gerarduscalcitrosus/shroompi/docs/camera_module.jpg

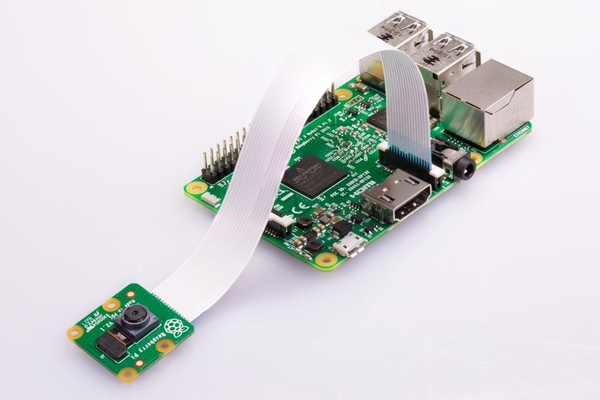
docs/camera_module.jpg
