gerarduscalcitrosus/shroompi/docs/prototypinghat.jpg

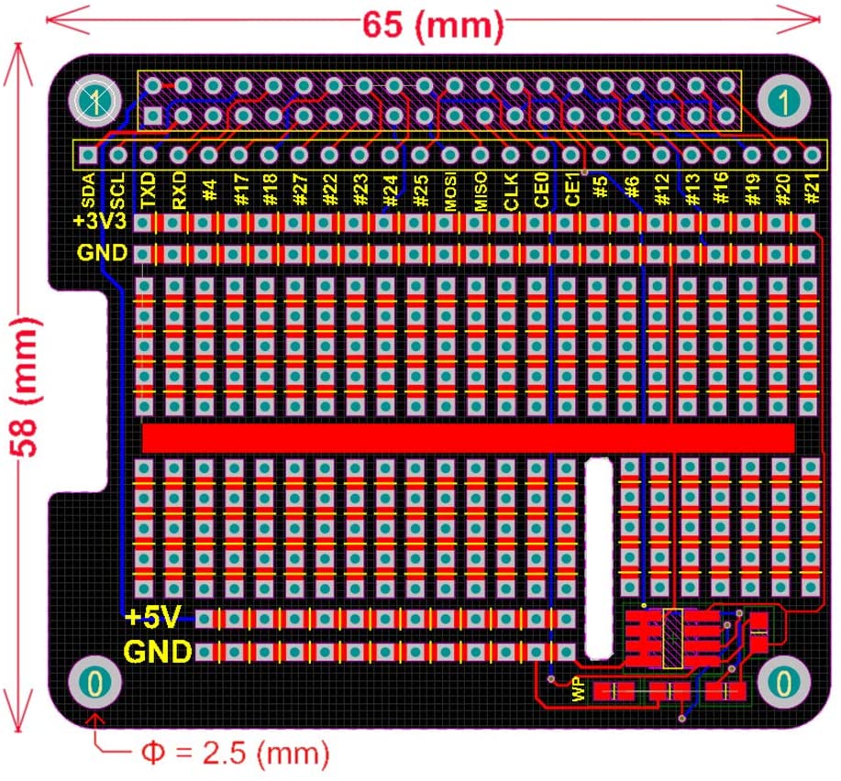
docs/prototypinghat.jpg
