gerarduscalcitrosus/shroompi/hardware/incubator/0_design.png

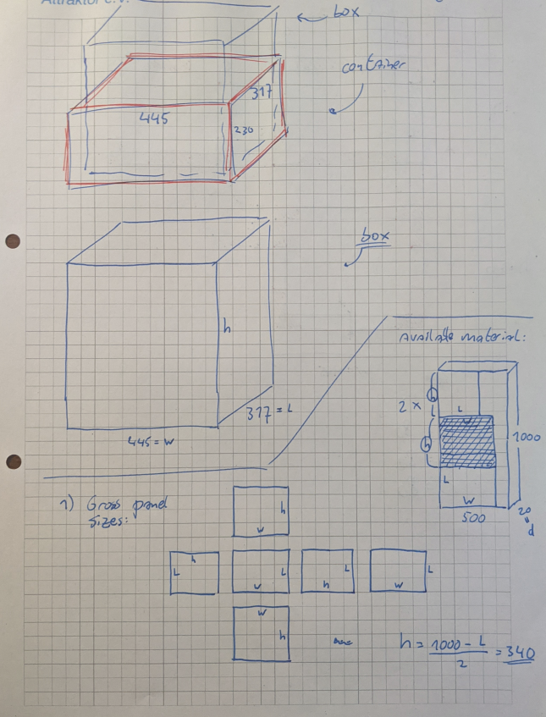
hardware/incubator/0_design.png
