gerarduscalcitrosus/shroompi/hardware/incubator/1_sizes.png

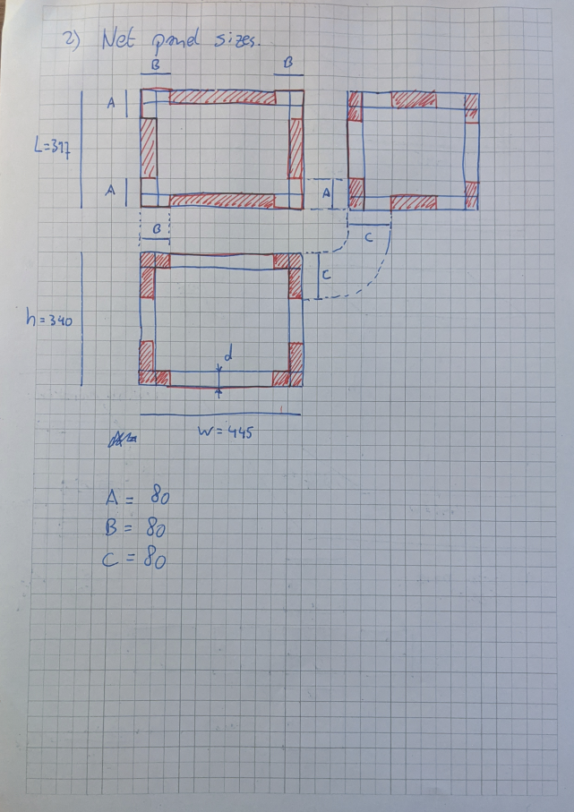
hardware/incubator/1_sizes.png
