gerarduscalcitrosus/shroompi/hardware/incubator/2_improvised_cutter.png

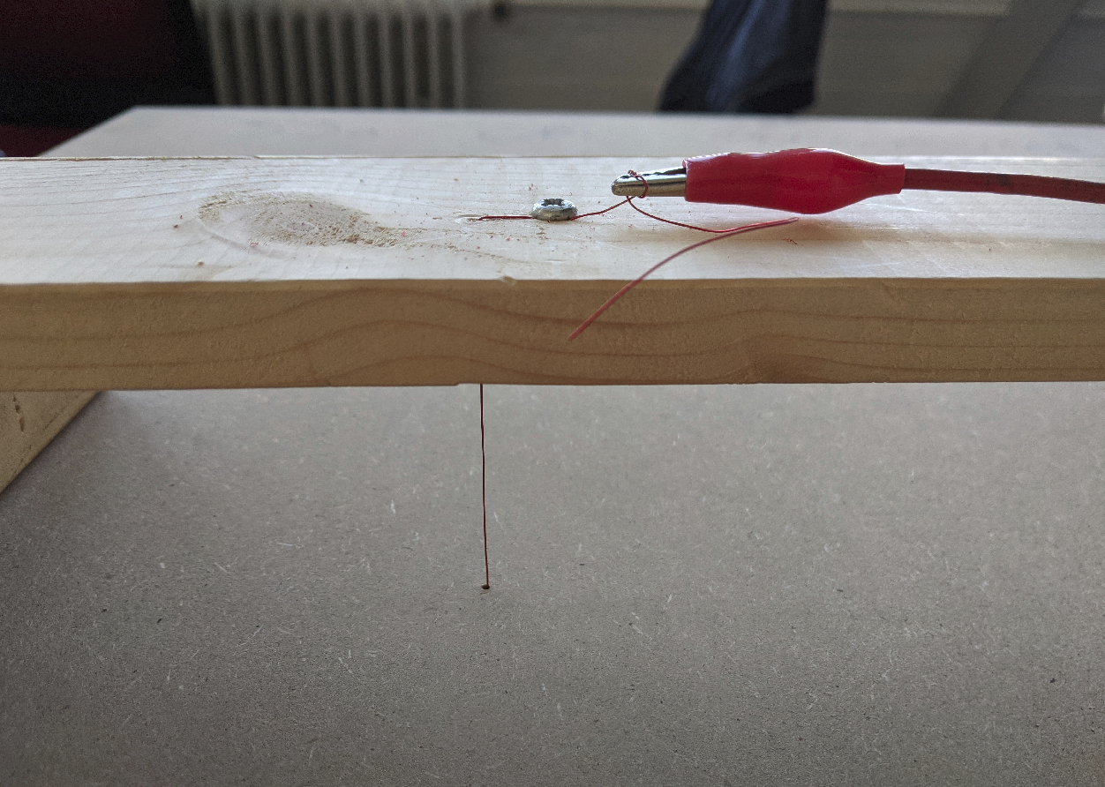
hardware/incubator/2_improvised_cutter.png
