gerarduscalcitrosus/shroompi/hardware/system/1_hardware.png

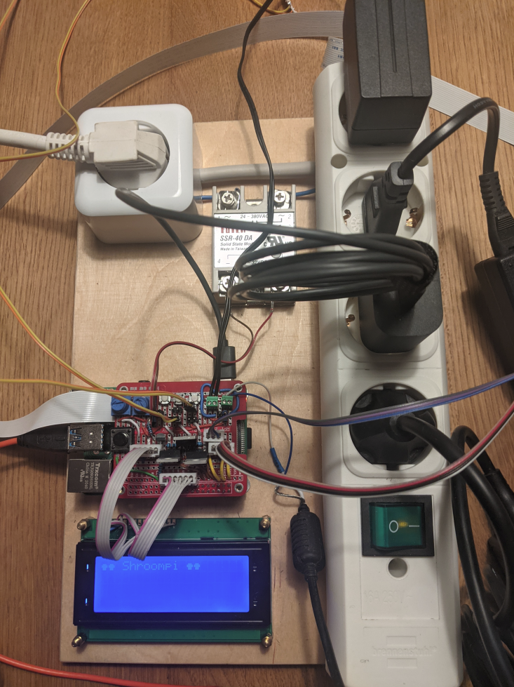
hardware/system/1_hardware.png
